mtarikucar/airpods-melek-seytan/out/airpods2/onizleme.png

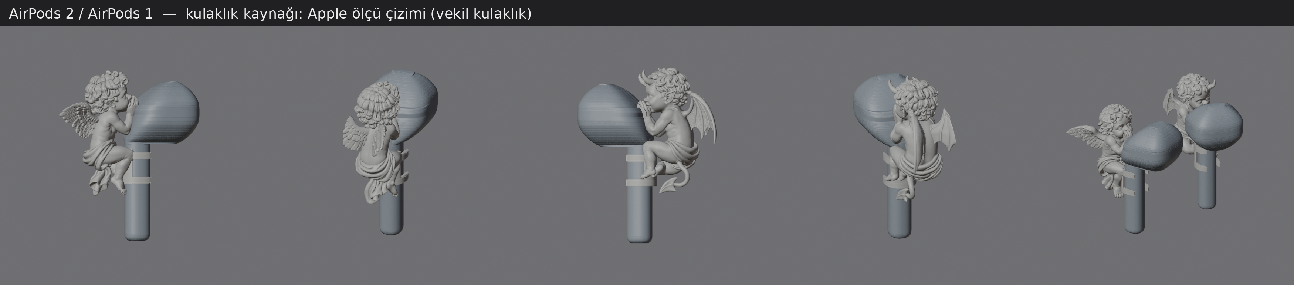
out/airpods2/onizleme.png
