mtarikucar/airpods-melek-seytan/out/airpods45/onizleme.png

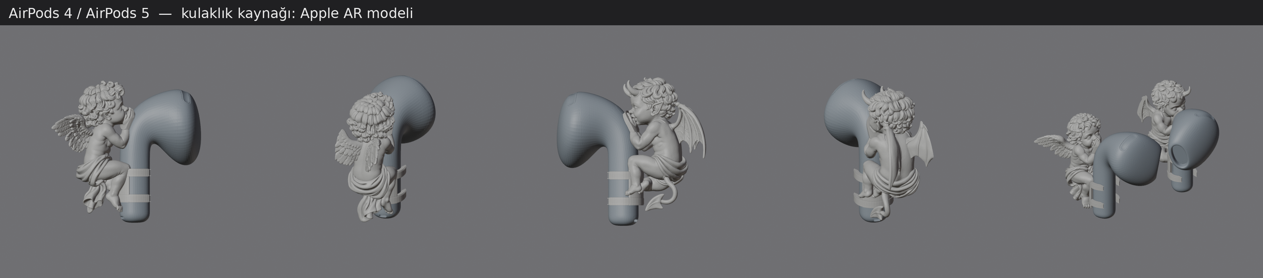
out/airpods45/onizleme.png
