mtarikucar/airpods-melek-seytan/out/ilan/gorseller/01_ana_gorsel.jpg

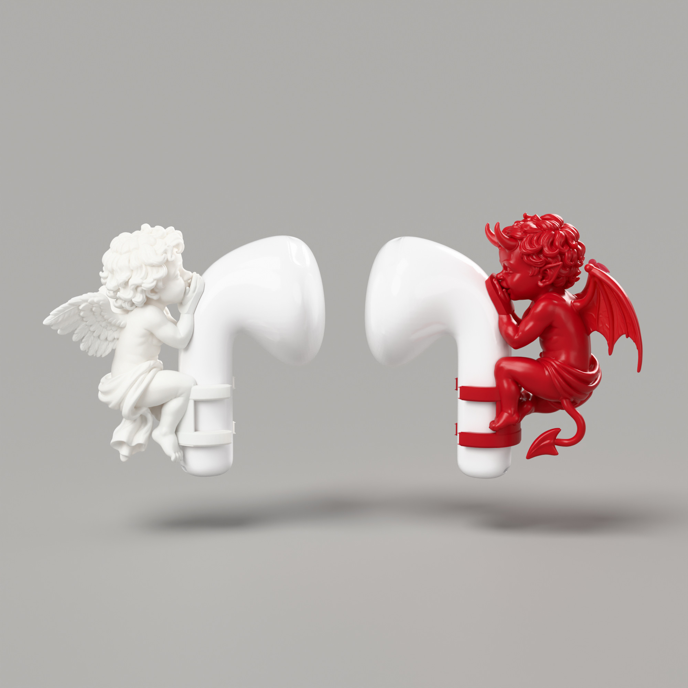
out/ilan/gorseller/01_ana_gorsel.jpg
