mtarikucar/airpods-melek-seytan/out/ilan/gorseller/02_melek_sag_kulaklik.jpg

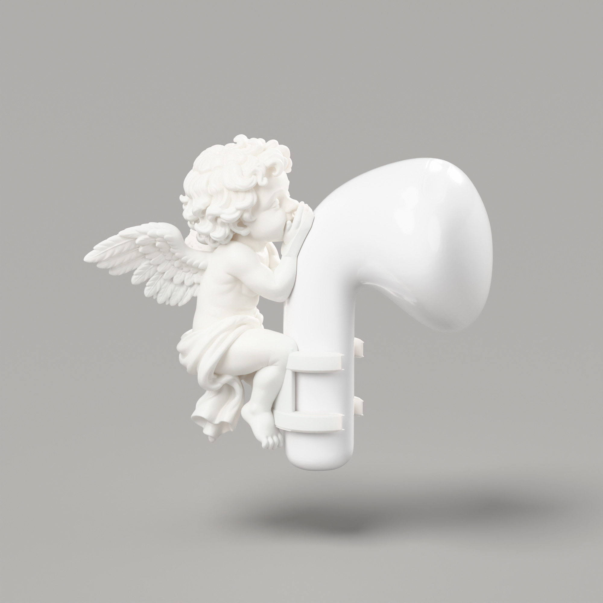
out/ilan/gorseller/02_melek_sag_kulaklik.jpg
