mtarikucar/airpods-melek-seytan/out/ilan/gorseller/03_seytan_sol_kulaklik.jpg

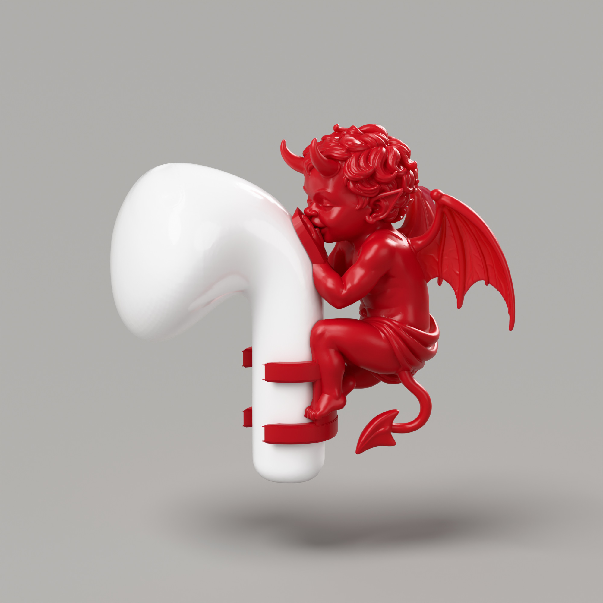
out/ilan/gorseller/03_seytan_sol_kulaklik.jpg
