mtarikucar/airpods-melek-seytan/out/ilan/gorseller/04_arkadan_gorunum.jpg

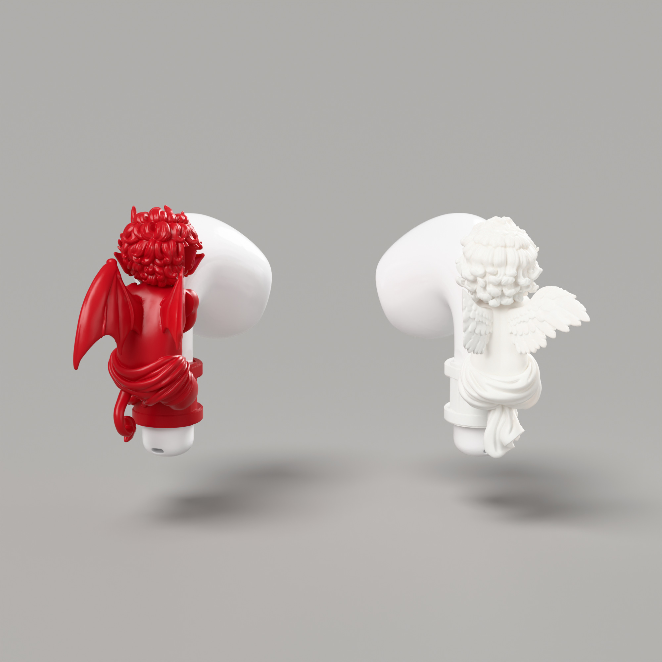
out/ilan/gorseller/04_arkadan_gorunum.jpg
