mtarikucar/airpods-melek-seytan/out/ilan/gorseller/05_detay_melek.jpg

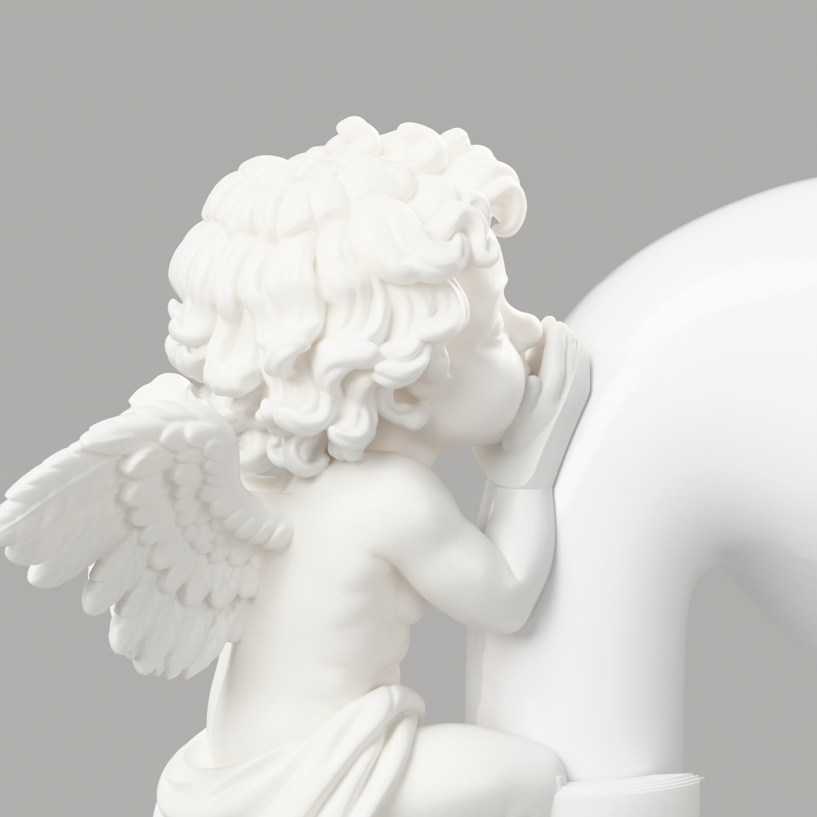
out/ilan/gorseller/05_detay_melek.jpg
