mtarikucar/airpods-melek-seytan/out/ilan/gorseller/07_figurler_kulakliksiz.jpg

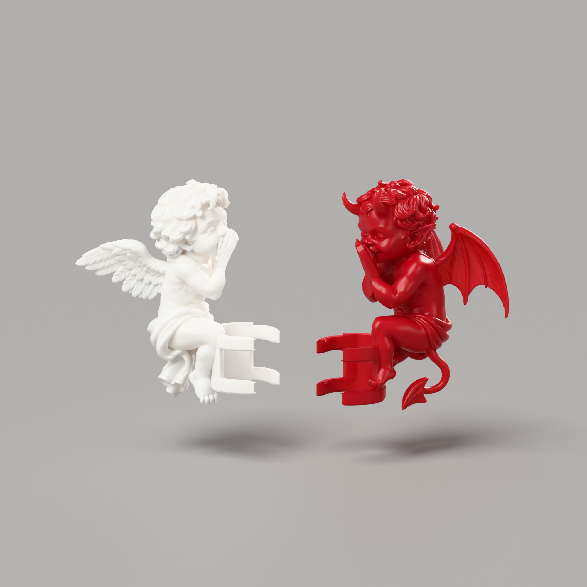
out/ilan/gorseller/07_figurler_kulakliksiz.jpg
