mtarikucar/airpods-melek-seytan/out/ilan/gorseller/08_olculer.jpg

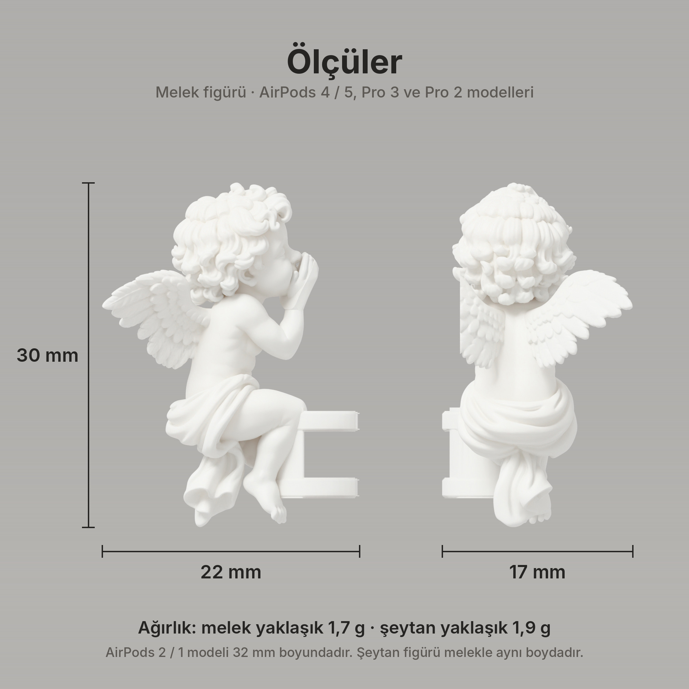
out/ilan/gorseller/08_olculer.jpg
