mtarikucar/airpods-melek-seytan/out/ilan/gorseller/10_nasil_takilir.jpg

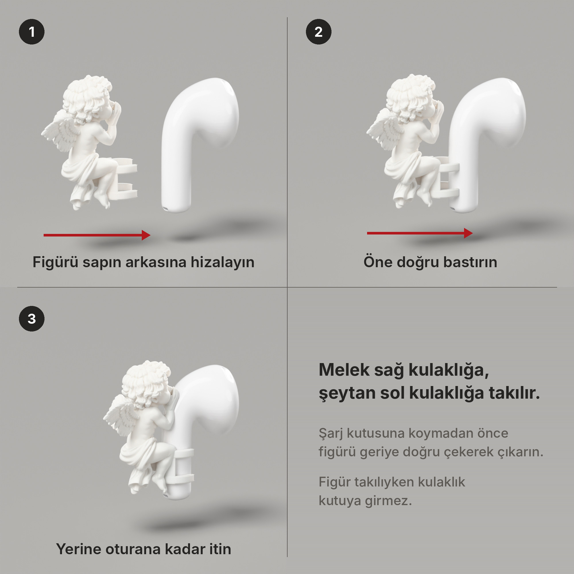
out/ilan/gorseller/10_nasil_takilir.jpg
