mtarikucar/airpods-melek-seytan/references/kulaklikli_konsept.png

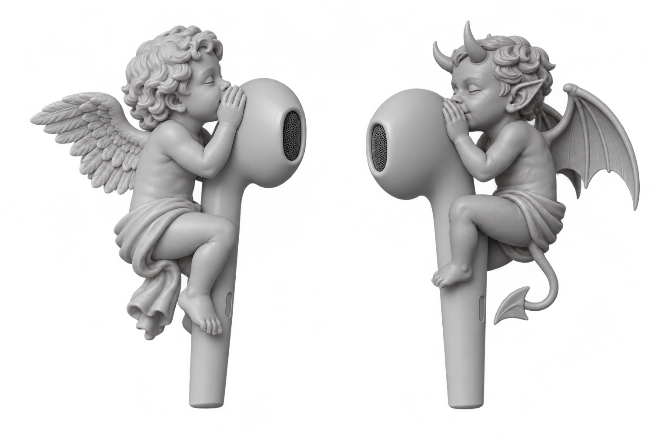
references/kulaklikli_konsept.png
