mtarikucar/airpods-melek-seytan/references/seytan.png

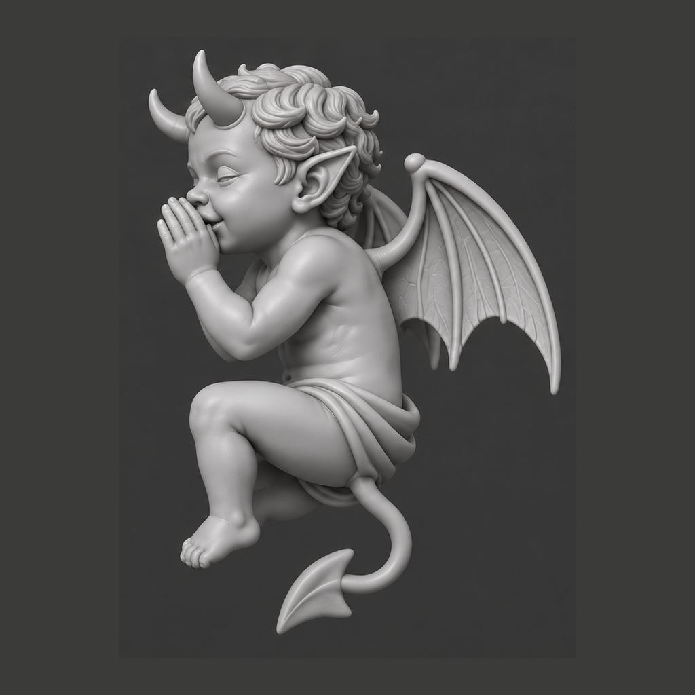
references/seytan.png
